77degrees/FlockOff/src/Flocker/cli_impl.h

/********************************************************************
 * cli_impl.h
 ********************************************************************
 * Command line handler implementation.  All command line handlers
 * are declared, defined, attached/bound, and implemented here.
 *******************************************************************/
#ifndef CLI_IMPL_H_
#define CLI_IMPL_H_

#include "globals.h"
#include "alloc.h"

#define CLI_BUFFER_SIZE_PS 8192
#define CLI_RX_BUFFER_SIZE_PS 1024
#define CLI_CMD_BUFFER_SIZE_PS 1024
#define CLI_HISTORY_SIZE_PS 64
#define CLI_BINDING_COUNT_PS 20

void onCommand(EmbeddedCli *embeddedCli, CliCommand *command);
void writeChar(EmbeddedCli *embeddedCli, char c);

/********************************************************
* Command line handler callback functions:
********************************************************/
// display build version and information
void onVersion(EmbeddedCli* cli, char* args, void* context);
const char* helpVersion = "version\r\n"
                          "Display version and build information\r\n\r\n";

// perform a manual device wireless survey
void onSurvey(EmbeddedCli* cli, char* args, void* context);
const char* helpSurvey = "survey [OPTION]\r\n"
                         "Perform a WiFi and/or Bluetooth survey.  Displays all results, not just those that match scan criteria.\r\n\r\n"
                         "  -i <INTERVAL>   interval in milliseconds to scan each WiFi channel\r\n"
                         "  -f <FILENAME>   save results to FILENAME in JSON format\r\n"
                         "  -n <NOTES>      add NOTES added for reference\r\n\r\n"
                         "If the -f parameter is not passed, JSON results will be displayed in the terminal.\r\n\r\n";

// Start scanning for matching devices
void onScan(EmbeddedCli* cli, char* args, void* context);
const char* helpScan = "scan [OPTION]\r\n"
                       "Start the continuous scan process, alerting via LEDs.\r\n\r\n"
                       "  -l <FILENAME>   log results to FILENAME, overrides config settings\r\n\r\n"
                       "Continuous scanning is the 'default' operating mode.  The device will continually monitor WiFi and BT signals; if a 'match' is found, the device will signal via flashing LEDSs.  Pressing any key in serial terminal will stop the scan.\r\n\r\n";


// clear terminal
void onClear(EmbeddedCli* cli, char* args, void* context);
const char* helpClear = "clear \r\n"
                        "Clear the serial console screen\r\n\r\n";

// reset device (close filesystem first)
void onReset(EmbeddedCli* cli, char* args, void* context);
const char* helpReset = "reset [OPTIONS]\r\n"
                        "Reboot the device, optionally performing a 'factory reset'\r\n"
                        "  --factory  perform a complete initialization on the device.\r\n"
                        "             All saved data will be lost and default configuration set\r\n\r\n";

// filesystem utils; ls, rm, mv, cp, cat
void onLs(EmbeddedCli* cli, char* args, void* context);
const char* helpLs = "ls [OPTIONS]\r\n"
                     "  -d   'dump' file - no console colors and delay after listing.  Use this option with script automation.\r\n"
                     "List files in the filesystem.  The device's filesystem is 'flat'; i.e., there are no directories.  Also note there are no parameters - all files are listed along with their size.\r\n\r\n";

void onDel(EmbeddedCli* cli, char* args, void* context);
const char* helpDel = "rm FILENAME\r\n"
                      "Delete FILENAME from filesystem.  One file at a time, with no globbing (no * or ? wildcards)\r\n\r\n";

void onMv(EmbeddedCli* cli, char* args, void* context);
const char* helpMv = "mv OLD_NAME NEW_NAME\r\n"
                    "Rename a file.\r\n\r\n";

void onCp(EmbeddedCli* cli, char* args, void* context);
const char* helpCp = "cp ORIGINAL_NAME COPY_NAME\r\n"
                     "Create a copy of a file in the filesystem.\r\n\r\n";

void onCat(EmbeddedCli* cli, char* args, void* context);
const char* helpCat = "cat [OPTIONS] FILENAME\r\n"
                      "List the contents of FILENAME in the console\r\n"
                      "  -d   'dump' file - no console colors and delay after listing.  Use this option with script automation.\r\n\r\n";

// write test file
void onWrite(EmbeddedCli* cli, char* args, void* context);
const char* helpWrite = "write FILENAME DATA\r\n"
                        "Create FILENAME in the filesystem and write arbitrary text DATA to it.\r\n\r\n";

// get system status
void onStatus(EmbeddedCli* cli, char* args, void* context);
const char* helpStatus = "status\r\n"
                         "Display system status which includes GPS status and location, filesytem capacity and usage, internal and PSRAM heap capacity and usage, and current local time and timezone.\r\n\r\n";

// interactive config stuff
void onConfig(EmbeddedCli* cli, char* args, void* context);
const char* helpConfig = "config [OPTION]\r\n"
                         "Set or display configuration parameters\r\n\r\n"
                         "  -l      display current configuration (dumps the raw JSON in pretty-print format)\r\n\r\n"
                         "If -l not given, show system configuration menu.\r\n\r\n";

// criteria config stuff
void onCriteria(EmbeddedCli* cli, char* args, void* context);
const char* helpCriteria = "criteria [OPTIONS]\r\n"
                           "Set or display target matching criteria\r\n\r\n"
                           "  -s   set default WiFi MAC prefix set\r\n"
                           "  -l   display wiFi MAC prefixes\r\n\r\n"
                           "This is a lot of stuff here \r\n\r\n";

/*******************************************************
* Binding struct for each command:
 struct CliCommandBinding {
    const char *name;       <--- command as entered on CLI
    const char *shortHelp;  <--- description shown with help command
    const char *help;       <--- detailed help shown with -h parameter on command
    bool tokenizeArgs;      <--- true if there are args
    void *context;          <--- data passed to handler if no args (not used here)
    void (*binding)(EmbeddedCli *cli, char *args, void *context);  <--- callback/command handler
  };
*******************************************************/
const struct CliCommandBinding bindings[] = {
  {"version", "Display firmware version", helpVersion, false, nullptr, onVersion},
  {"survey", "Perform WiFi survey", helpSurvey, true, nullptr, onSurvey},
  {"scan", "Start continuous scan", helpScan, true, nullptr, onScan},
  {"clear", "Clear the console", helpClear, false, nullptr, onClear},
  {"reset", "Reboot the device", helpReset, true, nullptr, onReset},
  {"ls", "List files", helpLs, true, nullptr, onLs},
  {"rm", "Delete file", helpDel, true, nullptr, onDel},
  {"write", "Write test file", helpWrite, true, nullptr, onWrite},
  {"mv", "Rename file", helpMv, true, nullptr, onMv},
  {"cp", "Copy file", helpCp, true, nullptr, onCp},
  {"cat", "Cat file", helpCat, true, nullptr,  onCat},
  {"status", "Get system status", helpStatus, false, nullptr, onStatus},
  {"config", "Get/Set config values", helpConfig, true, nullptr, onConfig},
  {"criteria", "Get/Set target matching criteria", helpCriteria, true, nullptr, onCriteria}};

const size_t bindingCount = sizeof(bindings) / sizeof(bindings[0]);

/******************************************************
* onCommand()
*******************************************************
* Command handler for unknown commands.  Just output
* an error message and remind user of 'help'
******************************************************/
void onCommand(EmbeddedCli *embeddedCli, CliCommand *command)
{
  Serial.printf("%sCommand not found: '%s'%s.  Use 'help' for command list.\r\n",
      CLI_BOLD_RED, command->name, CLI_RESET);

  flockLog.addLogLine("CLI", "Unknown command >%s<\r\n", command->name);
}

/******************************************************
* writeChar()
*******************************************************
* callback for CLI loop to know how to send chars back
* to user.  Serial, in this case
******************************************************/
void writeChar(EmbeddedCli *embeddedCli, char c)
{
  Serial.write(c);
}

/*****************************************************
 * callback for config command.  Either list the
 * config json file is listed, or the config handler
 * is called
 ****************************************************/
void onConfig(EmbeddedCli* cli, char* args, void* context)
{
  if (embeddedCliGetTokenCount(args) == 1)
  {
    const char* cmd = embeddedCliGetToken(args, 1);
    if (!strcmp("-l", cmd))
    {
      flockCfg.outputJson();
    }
  }
  else
  {
    flockCfg.setConfigValues();
  }
}

void onCriteria(EmbeddedCli* cli, char* args, void* context)
{
  if (embeddedCliGetTokenCount(args) == 1)
  {
    const char* cmd = embeddedCliGetToken(args, 1);
    if (!strcmp("-l", cmd))
    {
      Serial.printf(CLI_YEL "WiFi MAC match list has " CLI_BOLD_GRN "%d" CLI_RESET CLI_YEL " targets\r\n" CLI_RESET, scanTargets.getWiFiMacCount());
    }
    else if (!strcmp("-s", cmd))
    {
      Serial.printf(CLI_YEL "Set default WiFi MAC match list, " CLI_BOLD_GRN "%d" CLI_RESET CLI_YEL " targets\r\n", scanTargets.loadDefaultWiFiMacs());
    }
    else if (!strcmp("-x", cmd))
    {
      onStatus(cli, nullptr, nullptr);
      flk::string test;
      for (size_t ii = 0; ii < 5000; ++ii)
      {
        test += "abcdefghi";
      }
      onStatus(cli, nullptr, nullptr);
    }
  }
}


/******************************************************
* onVersion()
*******************************************************
* Command to display version and build date/time
*
* Parameters:
*   None
*
******************************************************/
void onVersion(EmbeddedCli* cli, char* args, void* context)
{
  Serial.printf(CLI_CYA "Flocker version " CLI_BOLD_GRN "%d.%d.%d" CLI_RESET CLI_CYA ", built on " CLI_BOLD_GRN "%s at %s\r\n" CLI_RESET,
    FLOCKER_VERSION_MAJOR, FLOCKER_VERSION_MINOR, FLOCKER_VERSION_SUBMINOR, FLOCKER_BUILD_DATE, FLOCKER_BUILD_TIME);
}

/******************************************************
* onSurvey()
*******************************************************
* Command to perform a single scan for wireless devices
* both WiFi and BLE.  Note that this will populate a
* results set with EVERYTHING seen, not just known
* Flock/survellance devices
*
* Parameters:
*   -h - show help
*   -i <interval> - how much time (in ms) to spend on
*                   each WiFi channel and on BLE
*   -f <filename> - save results to specified filename
*   -j <notes>    - save file as JSON (requires -f parameter)
*
******************************************************/
void onSurvey(EmbeddedCli* cli, char* args, void* context)
{
  bool paramErr = false;
  bool doFile = false;
  bool doJson = false;
  bool doBT = false;
  bool doWiFi = false;
  uint32_t interval = 1000;
  char fname[64] = {0};
  char notes[128] = {0};
  size_t argc = embeddedCliGetTokenCount(args);

  if (argc > 0)
  {
    for (size_t ii = 1; ii <= argc; ++ii)
    {
      const char* argv = embeddedCliGetToken(args, ii);

      if (strlen(argv) > 1)
      {
        if (argv[0] == '-')
        {
          if (argv[1] == 'n')
          {
            ++ii;
            if (ii <= argc)
            {
              argv = embeddedCliGetToken(args, ii);
              if (argv[0] == '-')
              {
                paramErr = true;
                break;
              }
              strncpy(notes, embeddedCliGetToken(args, ii), 127);
            }
            else
            {
              paramErr = true;
              break;
            }
          } // extracting notes
          else if (argv[1] == 'i')
          {
            ++ii;
            if (ii <= argc)
            {
              argv = embeddedCliGetToken(args, ii);
              if (argv[0] == '-')
              {
                paramErr = true;
                break;
              }
              interval = atoi(argv);
            }
            else
            {
              paramErr = true;
              break;
            }
          } // extracting interval
          else if (argv[1] == 'f')
          {
            ++ii;
            if (ii <= argc)
            {
              argv = embeddedCliGetToken(args, ii);
              if (argv[0] == '-')
              {
                paramErr = true;
                break;
              }
              strncpy(fname, embeddedCliGetToken(args, ii), 63);
            }
            else
            {
              paramErr = true;
              break;
            }
          } // extracting filename
          else
          {
            paramErr = true;
            break;
          }
        }
      }
      else
      {
        paramErr = true;
        break;
      }
    }
  }
  else
  {
    paramErr = true;
  }

  if (paramErr)
  {
    Serial.printf(CLI_BOLD_RED "Bad parameter." CLI_YEL "Usage: survey [-i <interval>] [-f <filename>] [-n <notes>].\r\n" CLI_RESET);
    return;
  }

  flockLog.addLogLine("CLI", "onSurvey()\r\n");
  flockScan.survey(interval, fname,notes);
}

/******************************************************
* onScan()
*******************************************************
* Command to start continuous scanning for wireless devices
* both WiFi and BLE.
*
* Parameters:
*   -l <filename> - save results to specified filename,
*                   overrides config settings
*
******************************************************/
void onScan(EmbeddedCli* cli, char* args, void* context)
{
    char logFileName[120] = {'\0'};

    if (embeddedCliGetTokenCount(args) == 2)
    {
        if (!strcmp(embeddedCliGetToken(args, 1), "-l"))
        {
            strncpy(logFileName, embeddedCliGetToken(args, 2), 119);
        }
        Serial.printf(CLI_BOLD_RED "Bad parameter: usage scan [-l <FILENAME>]\r\n" CLI_RESET);
    }

    flockScan.scan(logFileName);
}


/******************************************************
* onClear()
*******************************************************
* Command to clear the user's terminal (by sending
* ASCII code for that)
*
* Parameters:
*   None
*
******************************************************/
void onClear(EmbeddedCli *cli, char *args, void *context)
{
  flockLog.addLogLine("CLI", "onClear()\r\n");
  Serial.printf(CLI_CLEAR);
}

/******************************************************
* onLs()
*******************************************************
* Command to list files in the filesystem
*
* Parameters:
*   None
*
******************************************************/
void onLs(EmbeddedCli *cli, char *args, void *context)
{
  std::vector<flk::string>files;
  std::vector<flk::string>::const_iterator filesCit;
  bool dump = false;

  // call filesystem handler to populate all files and
  // shove them into our vector of files
  size_t count = flockfs.list(files);

  if (embeddedCliGetTokenCount(args) == 1)
  {
    // -d parameter means ls is being called in "dump" mode
    // no fancy colors or ANSII sequences
    if (!strcmp(embeddedCliGetToken(args, 1), "-d"))
    {
      dump = true;
    }
  }

  flockLog.addLogLine("CLI", "onLs(%s)\r\n", dump ? "dump" : "");

  if (!dump)
  {
    Serial.printf(CLI_GRN);
  }

  for (filesCit = files.begin(); filesCit != files.end(); ++filesCit)
  {
    // really inefficient, but how many files will there be, eh?
    Serial.printf(" %8d  %s  %s\r\n",
          flockfs.getFileSize(filesCit->c_str()), flockfs.lastFileWrite(filesCit->c_str()), filesCit->c_str());
  }

  if (dump)
  {
    delay(2000);
  }
  else
  {
    Serial.printf(CLI_RESET);
  }
}

/******************************************************
* onWrite()
*******************************************************
* Command to create a test file in the filesystem
*
* Parameters (positional):
*   <filename> <string to write to file>
*
* Example:
*   write test.txt "abc def ghi"
*
******************************************************/
void onWrite(EmbeddedCli *cli, char *args, void *context)
{
  if (embeddedCliGetTokenCount(args) == 2)
  {
    const char* fname = embeddedCliGetToken(args, 1);
    ssize_t len = flockfs.writeFile(fname, (uint8_t*)embeddedCliGetToken(args, 2), strlen(embeddedCliGetToken(args, 2)));

    if (len == -1)
    {
      Serial.printf(CLI_BOLD_RED "Error writing to %s\r\n" CLI_RESET, fname);
      flockLog.addLogLine("CLI", "onWrite() error writing to %s\r\n", fname);
    }
    else
    {
      Serial.printf(CLI_YEL "Wrote " CLI_BOLD_GRN "%d" CLI_RESET " " CLI_YEL " bytes to " CLI_BOLD_GRN "%s\r\n" CLI_RESET, len, fname);
      flockLog.addLogLine("CLI", "onWrite() wrote %d bytes to %s\r\n", len, fname);
    }
  }
  else
  {
    Serial.printf(CLI_BOLD_RED "Missing filename or data. " CLI_RESET " " CLI_YEL "Usage: write FILENAME DATA\r\n" CLI_RESET);
    flockLog.addLogLine("CLI", "onWrite() bad invocation\r\n");
  }
}

/******************************************************
* onDel()
*******************************************************
* Command to delete a file from the filesystem
*
* Parameters:
*   <file_to_delete>
*
******************************************************/
void onDel(EmbeddedCli* cli, char* args, void* context)
{
  if (embeddedCliGetTokenCount(args) == 1)
  {
    const char* fname = embeddedCliGetToken(args, 1);
    if (flockfs.deleteFile(fname))
    {
      Serial.printf(CLI_YEL "Deleted " CLI_BOLD_GRN "%s\r\n" CLI_RESET, fname);
      flockLog.addLogLine("CLI", "onDel() deleted %s\r\n", fname);
    }
    else
    {
      Serial.printf(CLI_BOLD_RED "Failed to delete " CLI_BOLD_GRN "%s\r\n" CLI_RESET, fname);
      flockLog.addLogLine("CLI", "onDel() error deleting %s\r\n", fname);
    }
  }
  else
  {
    Serial.printf(CLI_BOLD_RED "Missing filename. " CLI_YEL "Usage: rm FILENAME\r\n" CLI_RESET);
    flockLog.addLogLine("CLI", "onDel() invocation error\r\n");
  }
}

/******************************************************
* onMv()
*******************************************************
* Command to rename a file in the filesystem
*
* Parameters:
*   <original_name> <new_name>
*
******************************************************/
void onMv(EmbeddedCli* cli, char* args, void* context)
{
  if (embeddedCliGetTokenCount(args) == 2)
  {
    const char* fromName = embeddedCliGetToken(args, 1);
    const char* toName = embeddedCliGetToken(args, 2);

    if (flockfs.renameFile(fromName, toName))
    {
      Serial.printf(CLI_YEL "Renamed " CLI_BOLD_GRN "%s" CLI_YEL " to " CLI_BOLD_GRN "%s\r\n" CLI_RESET, fromName, toName);
      flockLog.addLogLine("CLI", "onMv() moved %s to %s\r\n", fromName, toName);
    }
    else
    {
      Serial.printf(CLI_BOLD_RED "Failed to rename " CLI_BOLD_GRN "%s\r\n" CLI_RESET, fromName);
      flockLog.addLogLine("CLI", "onMv() error in rename\r\n");
    }
  }
  else
  {
    Serial.printf(CLI_BOLD_RED "Missing filename(s). " CLI_YEL "Usage: MV OLDNAME NEWNAME\r\n" CLI_RESET);
    flockLog.addLogLine("CLI", "onMv() invocation error\r\n");
  }
}

/******************************************************
* onCp()
*******************************************************
* Command to copy a file in the filesystem
*
* Parameters:
*   <original_name> <copied_name>
*
******************************************************/
void onCp(EmbeddedCli* cli, char* args, void* context)
{
  if (embeddedCliGetTokenCount(args) == 2)
  {
    const char* fromName = embeddedCliGetToken(args, 1);
    const char* toName = embeddedCliGetToken(args, 2);

    if (flockfs.copyFile(fromName, toName))
    {
      Serial.printf(CLI_YEL "Copied " CLI_BOLD_GRN "%s" CLI_YEL " to " CLI_BOLD_GRN "%s\r\n" CLI_RESET, fromName, toName);
      flockLog.addLogLine("CLI", "onCp() copied %s to %s\r\n", fromName, toName);
    }
    else
    {
      Serial.printf(CLI_BOLD_RED "Failed to copy " CLI_BOLD_GRN "%s\r\n" CLI_RESET, fromName);
      flockLog.addLogLine("CLI", "onCp() failed to copy moved %s to %s\r\n", fromName, toName);
    }
  }
  else
  {
    Serial.printf(CLI_BOLD_RED "Missing filename(s). " CLI_YEL "Usage: cp FROM TO\r\n" CLI_RESET);
    flockLog.addLogLine("CLI", "onCp() invocation error\r\n");
  }
}

/******************************************************
* onCat()
*******************************************************
* Command to list a file's contents
*
* Parameters:
*   <filename>
*
******************************************************/
void onCat(EmbeddedCli *cli, char *args, void *context)
{
  const char* fname;
  bool dump = false;
  int tokens = embeddedCliGetTokenCount(args);

  if (tokens == 1 || tokens == 2)
  {
    for (int token = 1; token <= tokens; ++token)
    {
        // -d parameter means "dump" mode, no ANSII sequences
        // or colors
        if (!strcmp(embeddedCliGetToken(args, token), "-d"))
        {
            dump = true;
        }
        else
        {
            fname = embeddedCliGetToken(args, token);
        }
    }

    // get filesize for alloc size of buffer
    ssize_t fileLen = flockfs.getFileSize(fname);
    if (fileLen == -1)
    {
      Serial.printf(CLI_BOLD_RED "File %s not found.\r\n" CLI_RESET, fname);
      return;
    }

    char* buf = (char*)ps_malloc(fileLen + 1);
    if (buf)
    {
      memset(buf, 0, fileLen + 1);
      size_t read = flockfs.readFile(fname, (uint8_t*)buf, fileLen);

      if (!dump)      Serial.printf(CLI_CYA);
      Serial.printf((char*)buf);
      if (!dump)      Serial.printf(CLI_RESET "\r\n");

      free(buf);
      flockLog.addLogLine("CLI", "onCat() listed contents of %s (%d bytes)\r\n", fname, read);
    }
    else
    {
      Serial.printf("DID NOT ALLOCATE PSRAM\r\n");
      flockLog.addLogLine("CLI", "onCat() failed to allocate psram\r\n");
    }
  }
  else
  {
    Serial.printf(CLI_BOLD_RED "Missing filename." CLI_YEL " Usage: cat [-d] FILENAME\r\n" CLI_RESET);
    flockLog.addLogLine("CLI", "onMv() invocation error\r\n");
  }

  if (dump)
  {
    delay(3000);
    Serial.printf("\r\n");
  }
}

/******************************************************
* onReset()
*******************************************************
* Command to reboot the system.  Will unmount filesytem
* before rebooting, so there is a slight delay
*
* if --factory is passed with the command, do a factory
* reset before restarting
*
******************************************************/
void onReset(EmbeddedCli *cli, char *args, void *context)
{
  flockLog.addLogLine("CLI", "onReset() shutting down!\r\n");
  flockLog.flushNow();

  if (embeddedCliGetTokenCount(args) == 1)
  {
    if (!strcmp(embeddedCliGetToken(args, 1), "--factory"))
    {
      flockfs.format();
      delay(500);
    }
  }
  LittleFS.end();
  delay(1000);

  ESP.restart();
}

/******************************************************
* onStatus()
*******************************************************
* Command to display system status.  This includes
*   GPS status
*   Filesystem status
*   Memory (heaps) status
*   Real time clock and timezone status
*
* Parameters:
*   None
*
******************************************************/
void onStatus(EmbeddedCli* cli, char* args, void* context)
{
  Serial.printf(CLI_CYA "->Hardware:\r\n" CLI_RESET);
  Serial.printf(CLI_YEL "\tChip model " CLI_BOLD_GRN "%s\r\n" CLI_RESET, ESP.getChipModel());
  Serial.printf(CLI_YEL "\tChip frequency " CLI_BOLD_GRN "%d MHz\r\n" CLI_RESET, ESP.getCpuFreqMHz());
  Serial.printf(CLI_YEL "\tCore count " CLI_BOLD_GRN "%d cores\r\n" CLI_RESET, ESP.getChipCores());
  Serial.printf(CLI_CYA "->GPS:\r\n" CLI_RESET);

  if (gps.getFixQuality() > 0)
  {
    struct tm tm_;
    gps.getTime(&tm_);
    Serial.printf(CLI_YEL "\tGPS current coordinates are " CLI_BOLD_GRN "%02.5f, %03.5f\r\n" CLI_RESET,
              gps.getLatitude(), gps.getLongitude());

    Serial.printf(CLI_YEL "\tGPS current time/date (gmt) is " CLI_BOLD_GRN "%02d:%02d:%02d %d/%d/%d\r\n" CLI_RESET,
              tm_.tm_hour, tm_.tm_min, tm_.tm_sec,
              tm_.tm_mon + 1, tm_.tm_mday, tm_.tm_year + 1900);

    Serial.printf(CLI_YEL "\tNumber of satellites currently tracked: " CLI_BOLD_GRN "%d\r\n" CLI_RESET, gps.getSatelliteCount());
  }
  else
  {
    Serial.printf(CLI_BOLD_RED "\tNo GPS position fix\r\n" CLI_RESET);
  }

  Serial.printf(CLI_CYA "->Filesystem:\r\n" CLI_RESET);
  size_t cap;
  size_t used;
  flockfs.getInfo(&cap, &used);
  Serial.printf(CLI_YEL "\tTotal capacity " CLI_BOLD_GRN "%d" CLI_RESET CLI_YEL " bytes, "
                CLI_BOLD_GRN "%d" CLI_RESET " " CLI_YEL "used (" CLI_BOLD_GRN "%d" CLI_RESET " " CLI_YEL "KiB free)\r\n" CLI_RESET,
                cap, used, (cap - used) / 1024);

  Serial.printf(CLI_CYA "->Memories:\r\n" CLI_RESET);
  Serial.printf(CLI_YEL "\tInternal total heap " CLI_BOLD_GRN "%d" CLI_RESET CLI_YEL " bytes, " CLI_BOLD_GRN "%d"
                CLI_RESET " " CLI_YEL "used (" CLI_BOLD_GRN "%d" CLI_RESET CLI_YEL " KiB free)\r\n" CLI_RESET,
                ESP.getHeapSize(), (ESP.getHeapSize() - ESP.getFreeHeap()), ESP.getFreeHeap() / 1024);
  Serial.printf(CLI_YEL "\tPSRAM total heap " CLI_BOLD_GRN "%d" CLI_RESET CLI_YEL " bytes, " CLI_BOLD_GRN "%d"
                CLI_RESET " " CLI_YEL "used (" CLI_BOLD_GRN "%d" CLI_RESET CLI_YEL " KiB free)\r\n" CLI_RESET,
                ESP.getPsramSize(), (ESP.getPsramSize() - ESP.getFreePsram()), ESP.getPsramSize() / 1024);

  Serial.printf(CLI_CYA "->Wall clock:\r\n" CLI_RESET);
  char tstring[64] = {0};

  time_t t = time(NULL);
  tm *tmp;
  tmp = localtime(&t);

  strftime(tstring, 63, "%a, %d %b %Y %T %z", tmp);
  Serial.printf(CLI_YEL "\tCurrent wall clock time is " CLI_BOLD_GRN "%s\r\n" CLI_RESET, tstring);
  Serial.printf(CLI_YEL "\tTimezone is set to " CLI_BOLD_GRN "%s\r\n" CLI_RESET, flockCfg.getTimeZone());

  flockLog.addLogLine("CLI", "onStatus()\r\n");
}


#endif // CLI_IMPL_H_
